erhelito/TIPE-LIFI/pics/IMG_20250205_171345.jpg

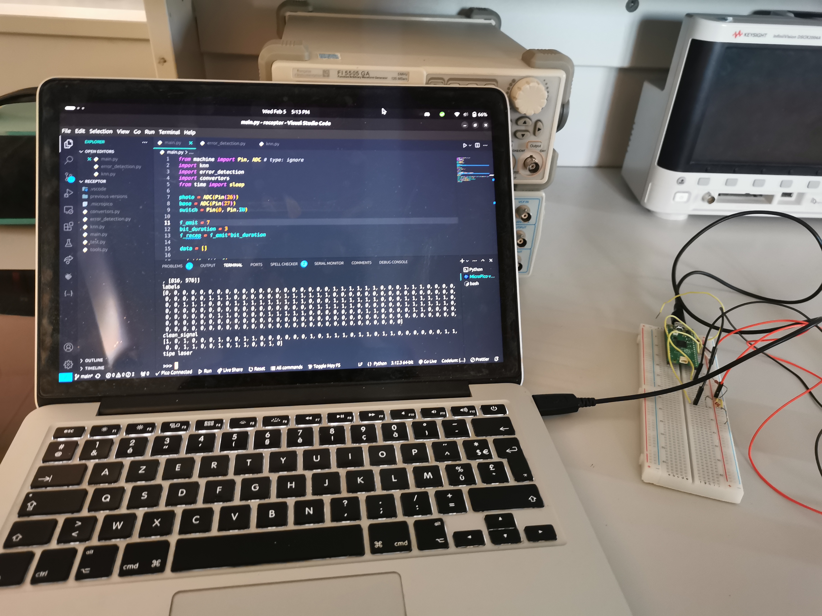
pics/IMG_20250205_171345.jpg
