erhelito/TIPE-LIFI/pics/IMG_20250509_170922.jpg

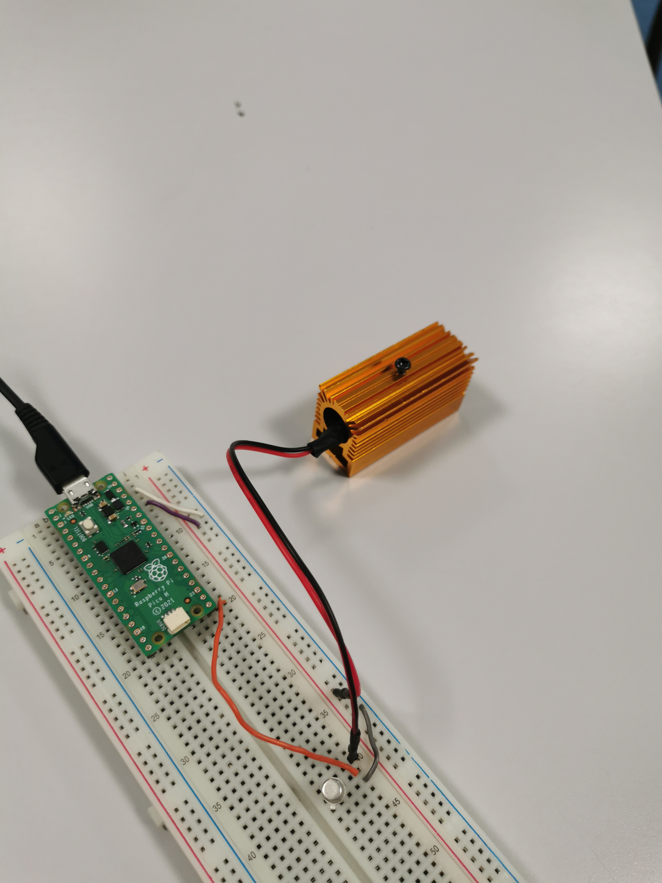
pics/IMG_20250509_170922.jpg
