erhelito/TIPE-LIFI/3D/supports.png

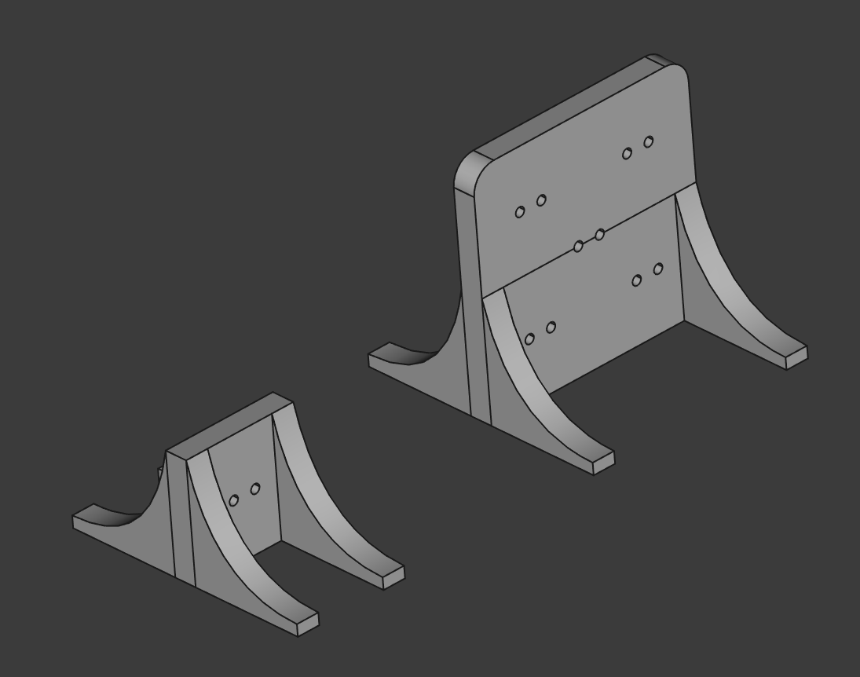
3D/supports.png
