erhelito/TIPE-LIFI/lifi elec/emitter.png

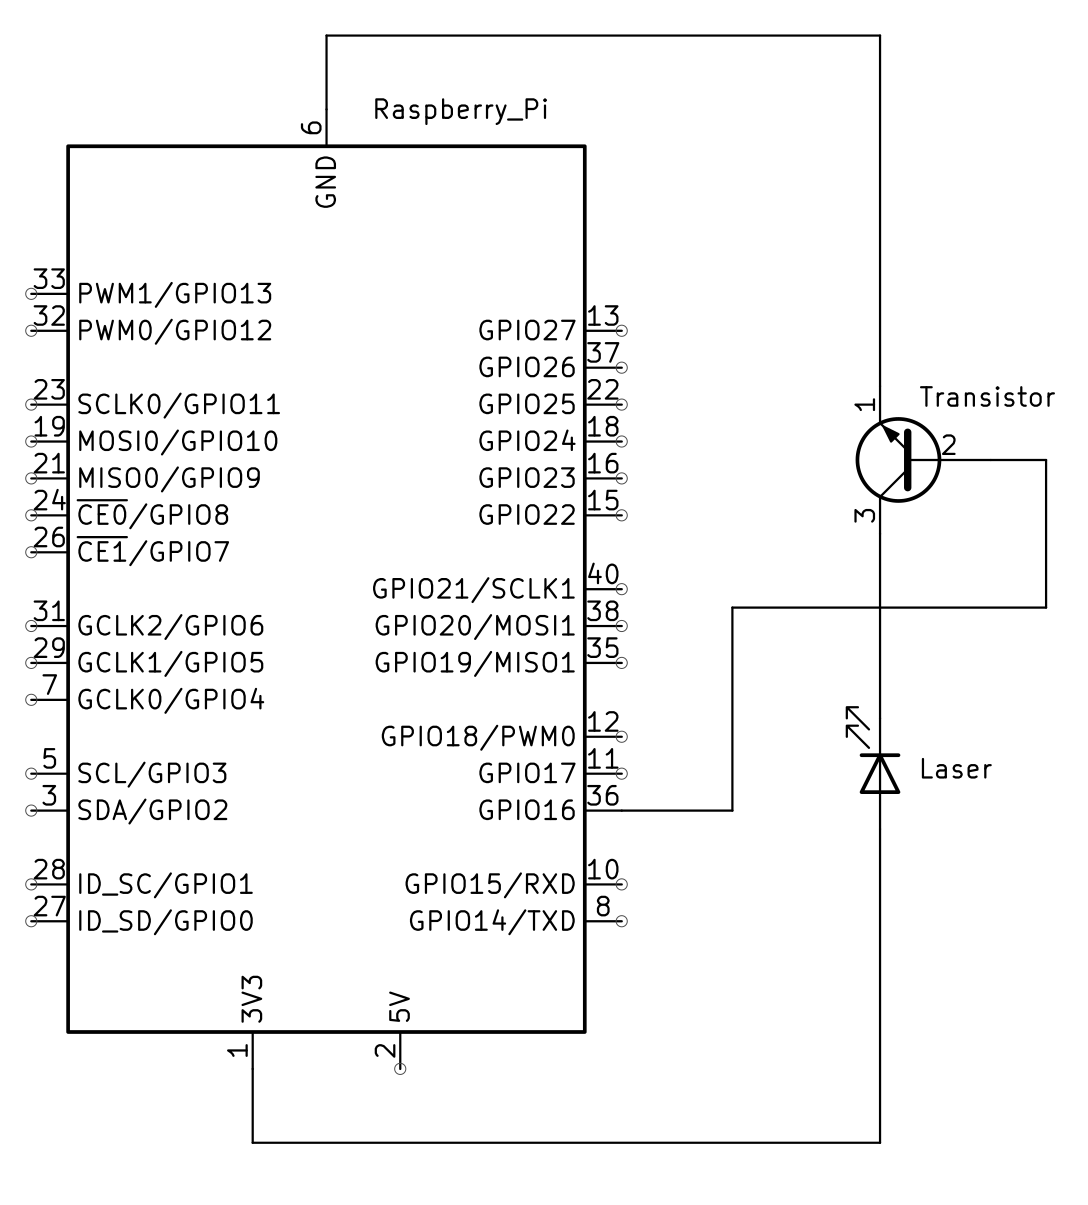
lifi elec/emitter.png
