erhelito/TIPE-LIFI/pics/IMG_20250129_170748.jpg

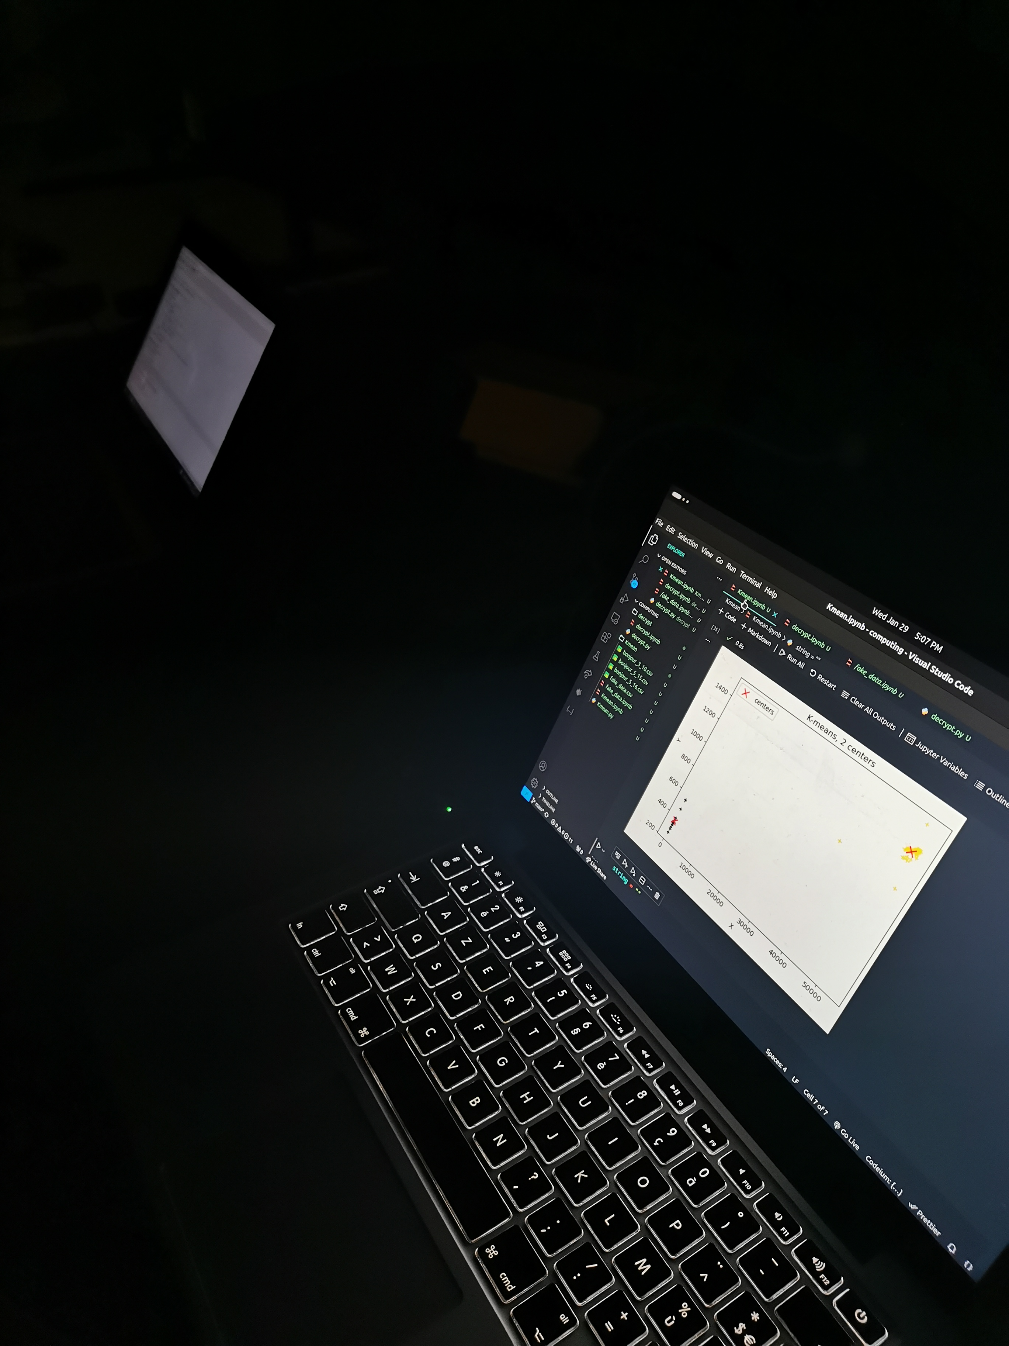
pics/IMG_20250129_170748.jpg
