erhelito/TIPE-LIFI/pics/IMG_20250129_170801.jpg

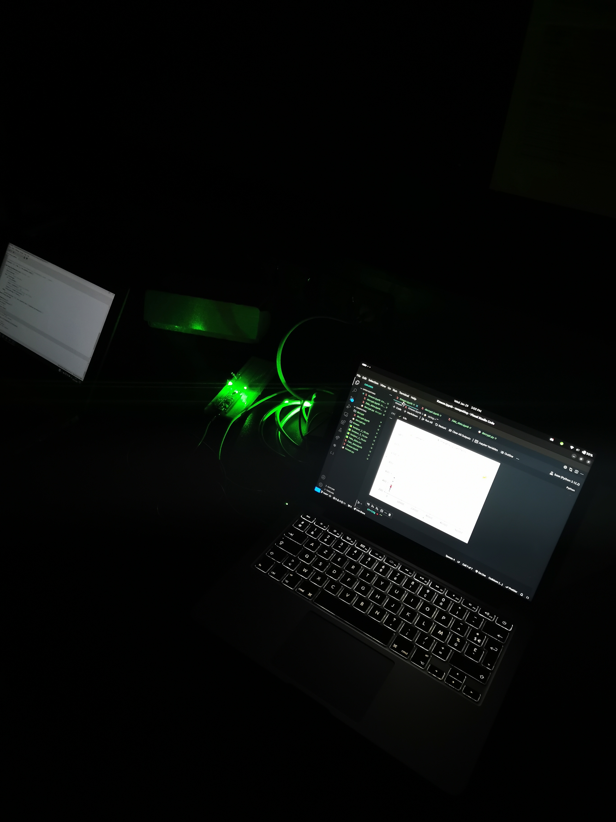
pics/IMG_20250129_170801.jpg
