erhelito/TIPE-LIFI/pics/IMG_20250129_170805.jpg

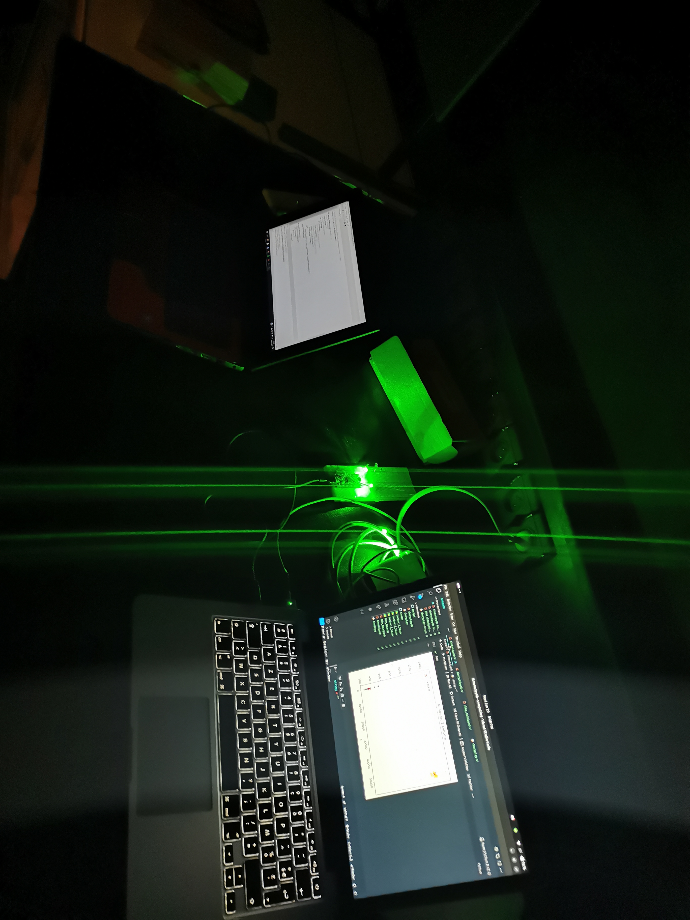
pics/IMG_20250129_170805.jpg
