erhelito/TIPE-LIFI/pics/IMG_20250205_155208.jpg

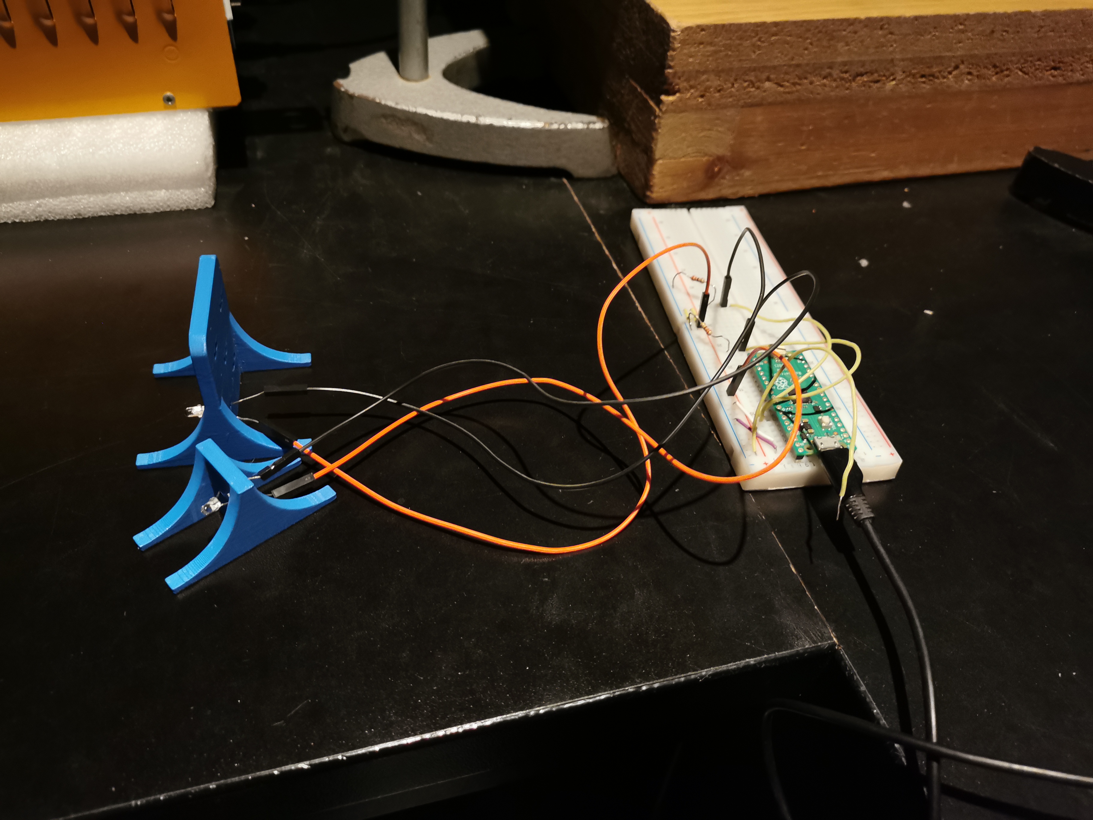
pics/IMG_20250205_155208.jpg
