erhelito/TIPE-LIFI/pics/IMG_20250205_171258.jpg

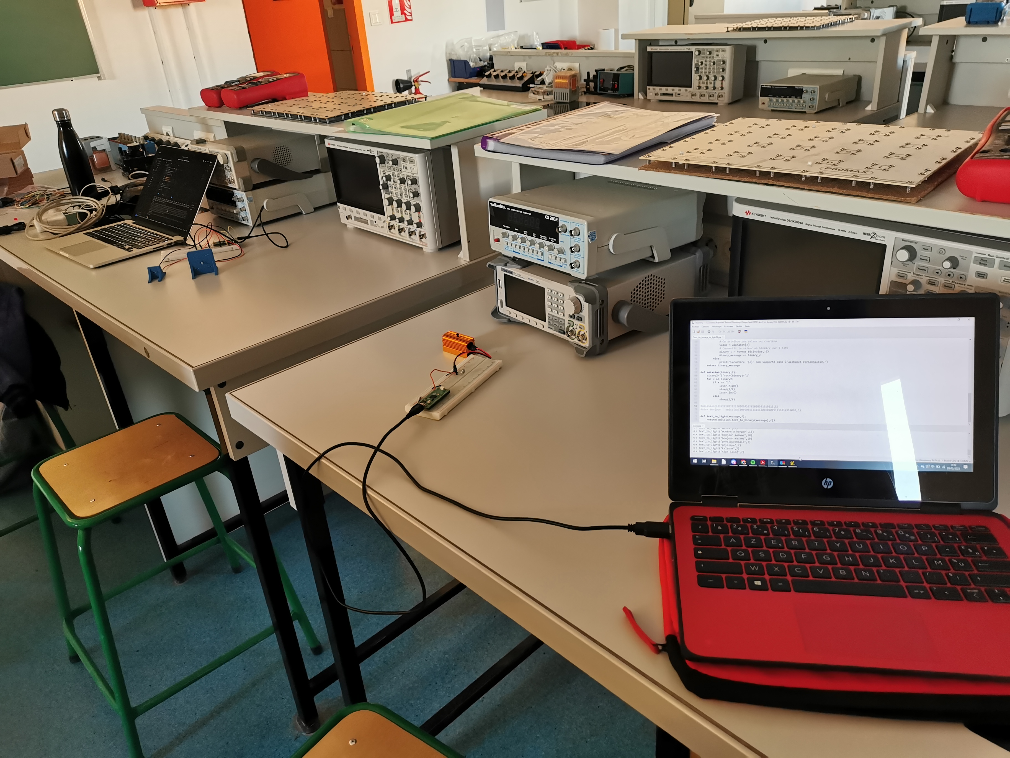
pics/IMG_20250205_171258.jpg
