erhelito/TIPE-LIFI/pics/IMG_20250205_171304.jpg

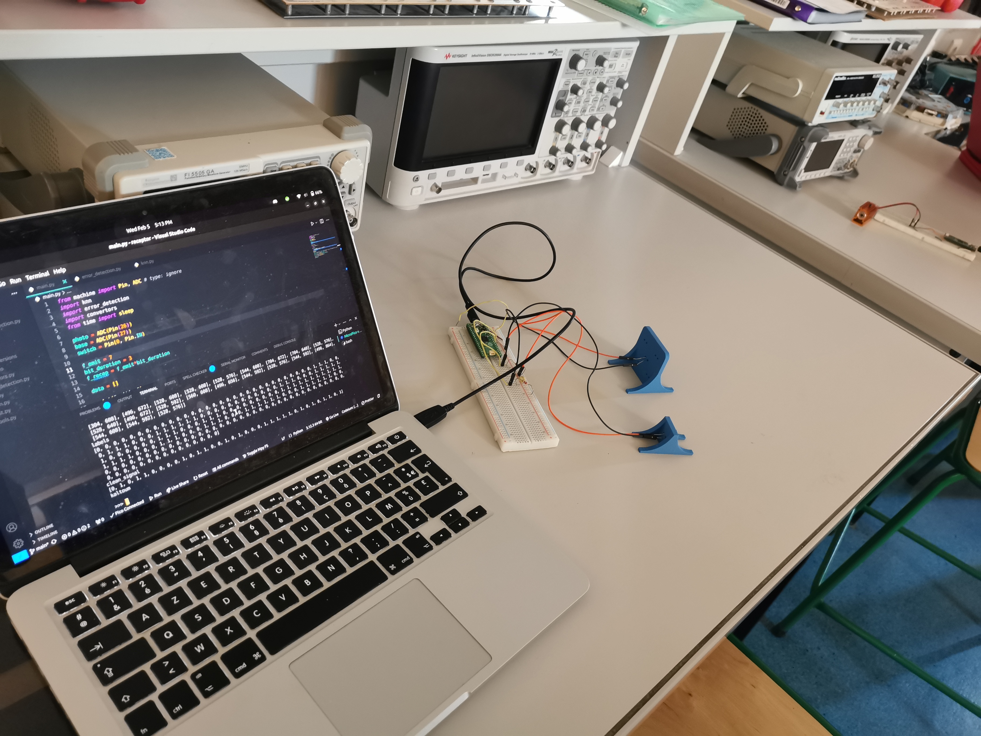
pics/IMG_20250205_171304.jpg
