erhelito/TIPE-LIFI/pics/IMG_20250205_171339.jpg

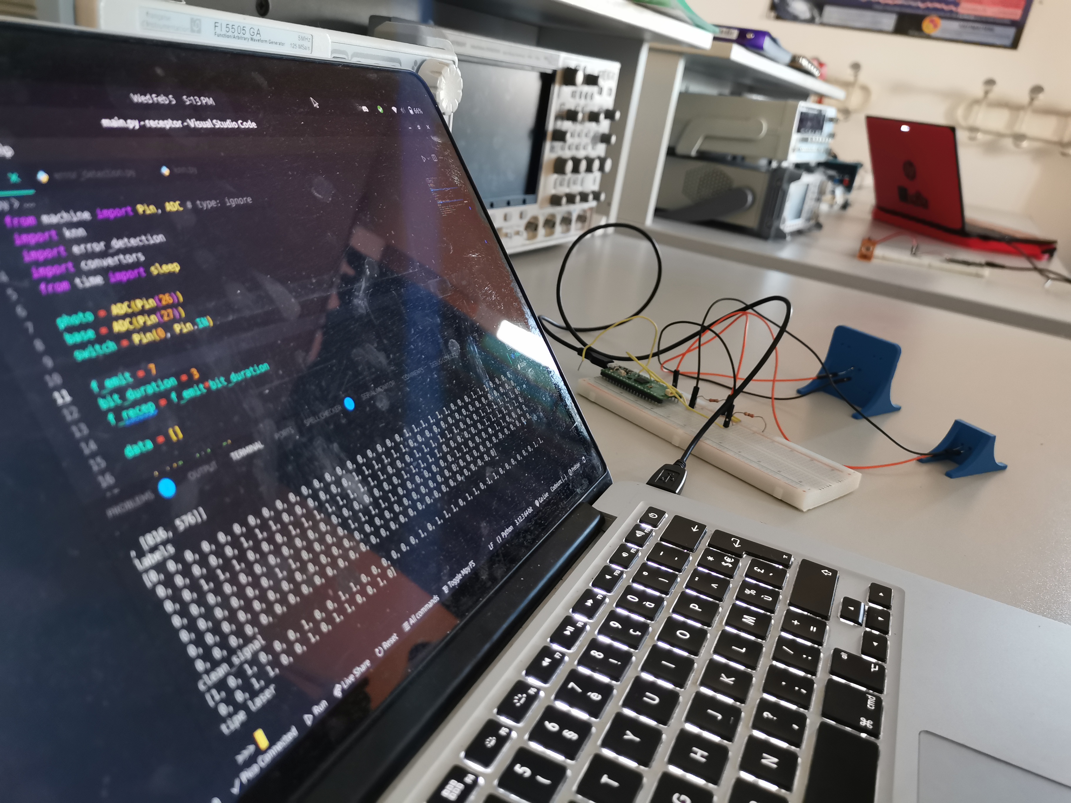
pics/IMG_20250205_171339.jpg
