erhelito/TIPE-LIFI/pics/IMG_20250205_171351.jpg

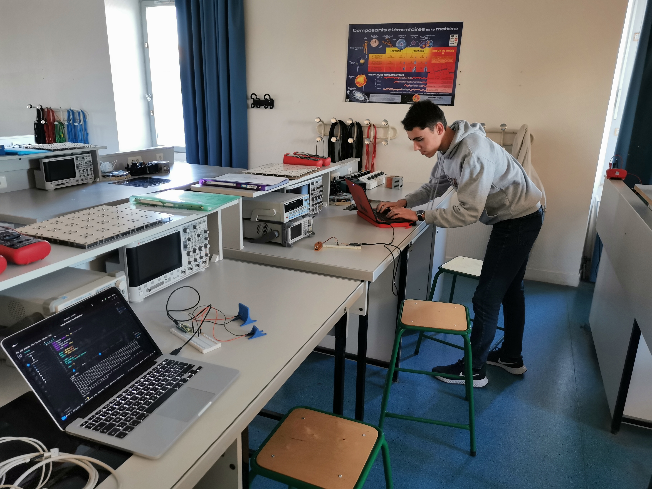
pics/IMG_20250205_171351.jpg
