erhelito/TIPE-LIFI/pics/IMG_20250212_154658.jpg

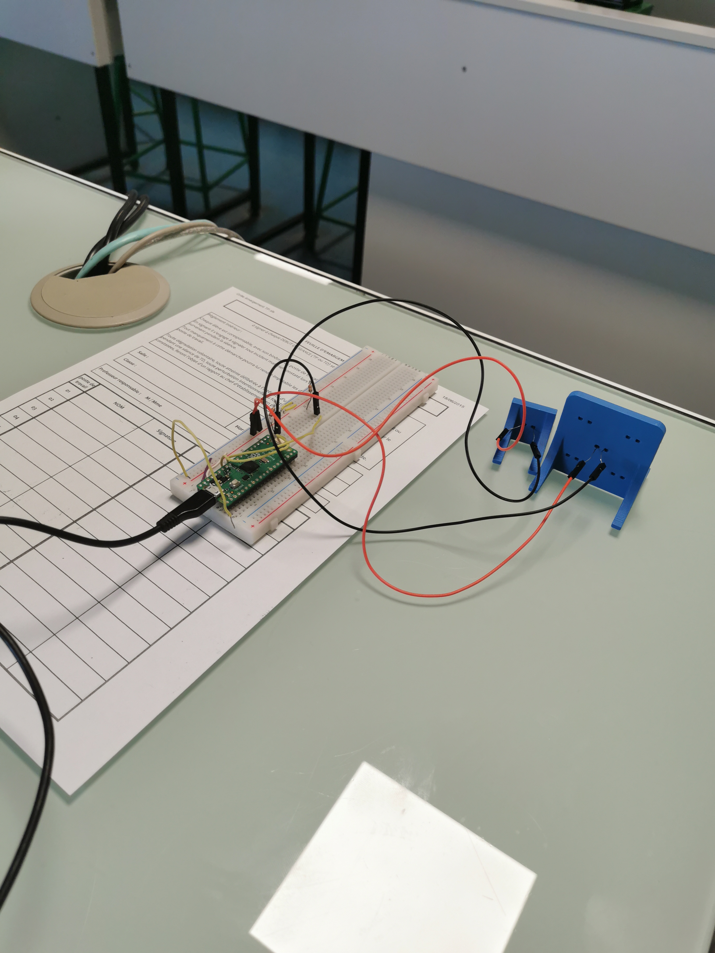
pics/IMG_20250212_154658.jpg
