erhelito/TIPE-LIFI/pics/IMG_20250212_154738.jpg

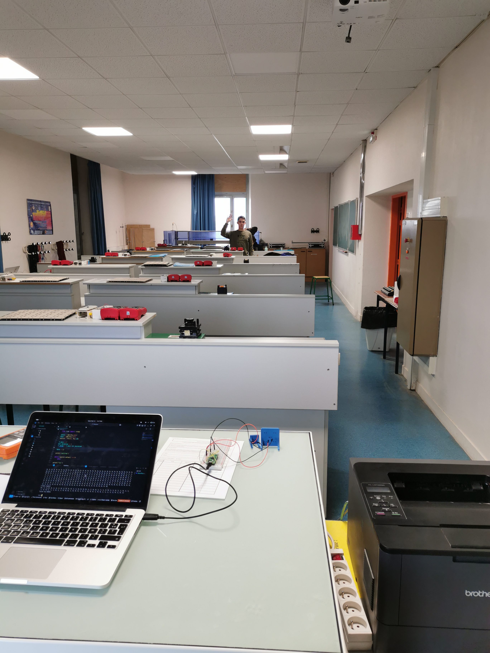
pics/IMG_20250212_154738.jpg
