erhelito/TIPE-LIFI/pics/IMG_20250212_160646.jpg

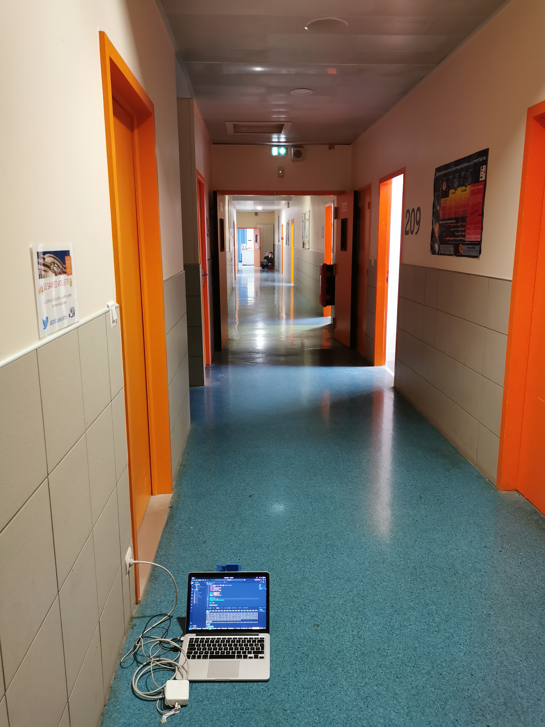
pics/IMG_20250212_160646.jpg
