erhelito/TIPE-LIFI/pics/IMG_20250305_170117.jpg

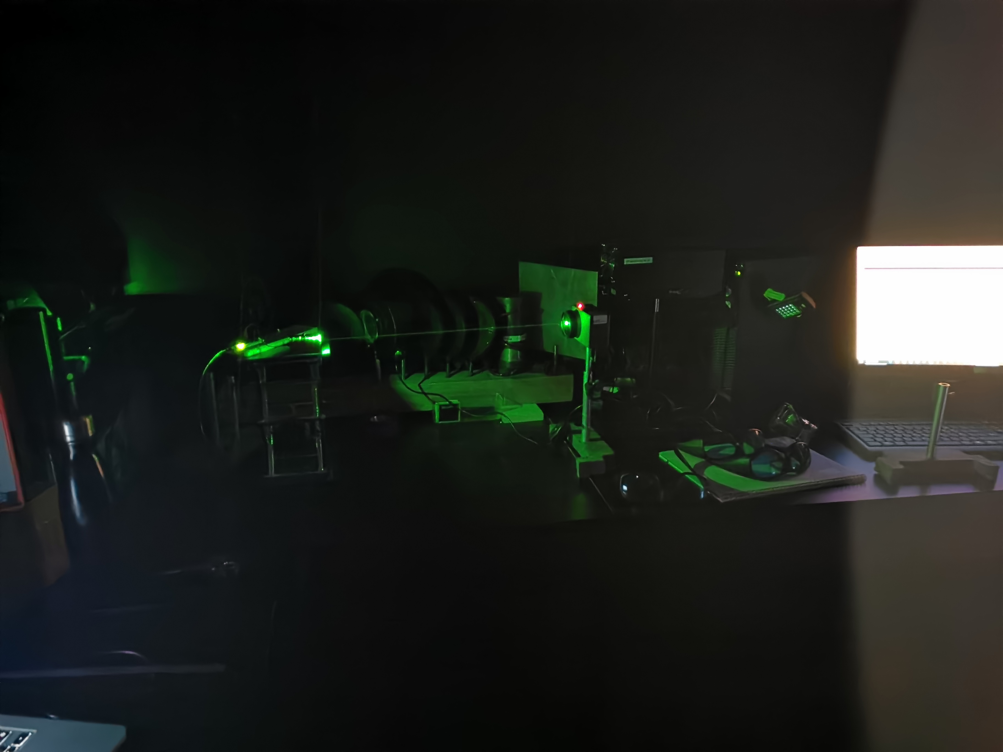
pics/IMG_20250305_170117.jpg
