erhelito/TIPE-LIFI/pics/IMG_20250319_162206.jpg

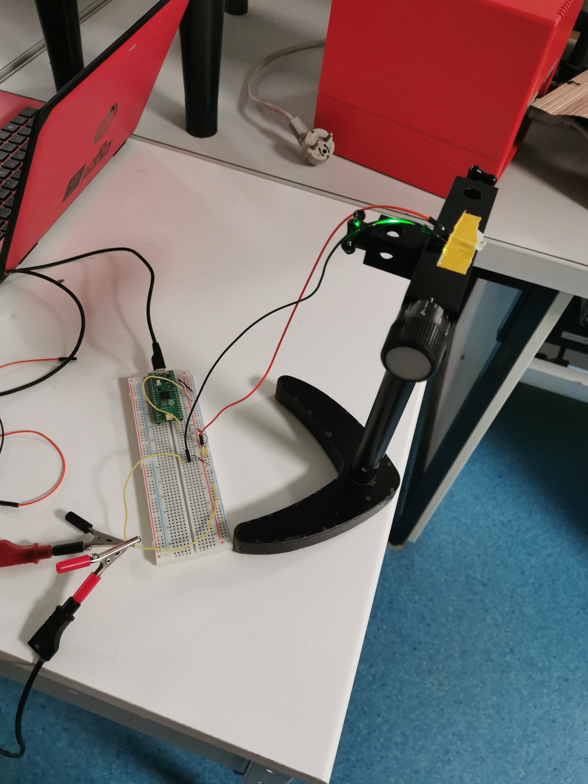
pics/IMG_20250319_162206.jpg
