erhelito/TIPE-LIFI/pics/IMG_20250319_162211.jpg

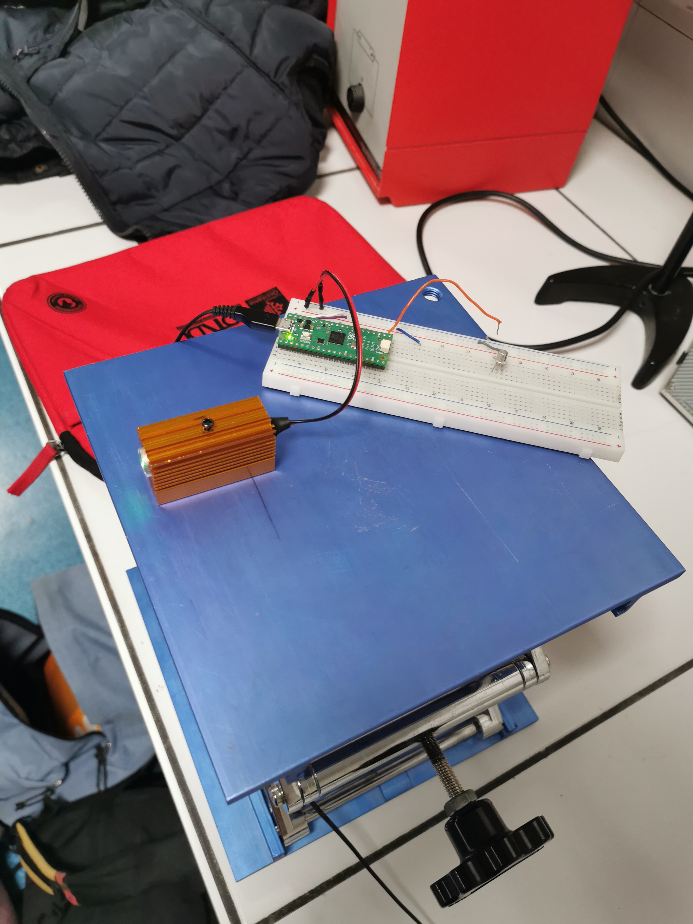
pics/IMG_20250319_162211.jpg
