erhelito/TIPE-LIFI/pics/IMG_20250319_164810.jpg

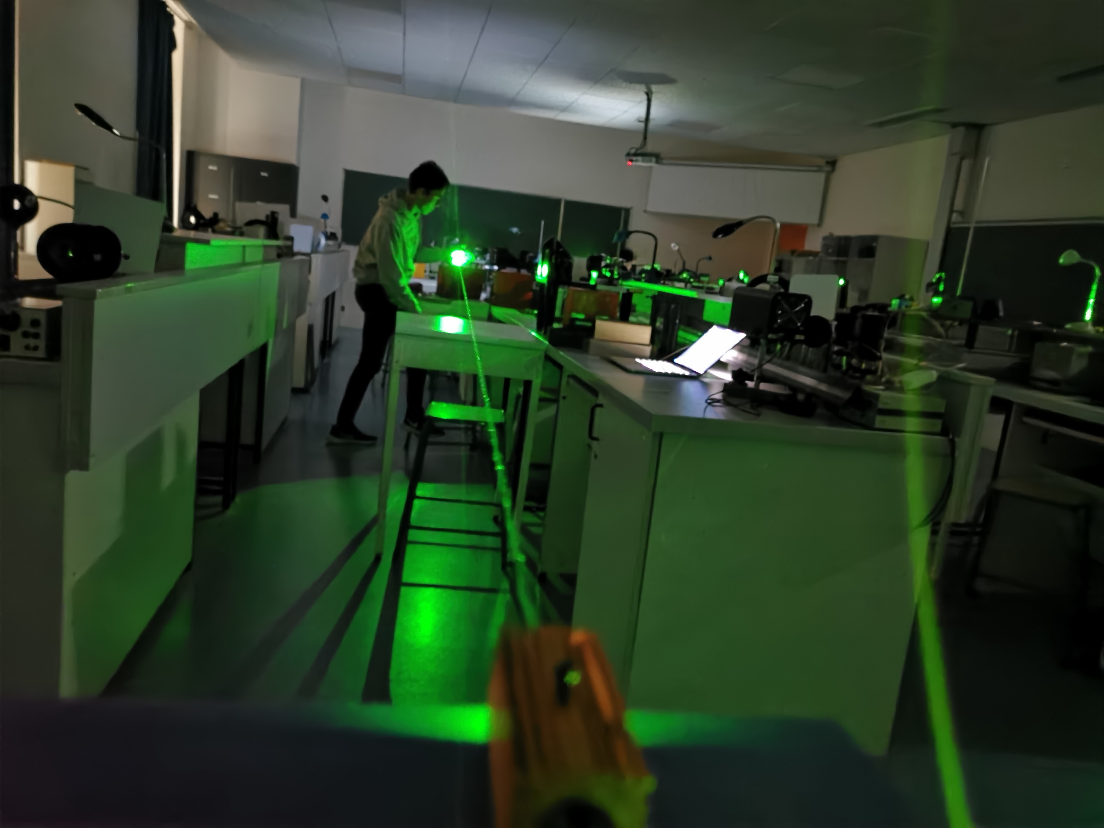
pics/IMG_20250319_164810.jpg
