erhelito/TIPE-LIFI/pics/IMG_20250509_170928.jpg

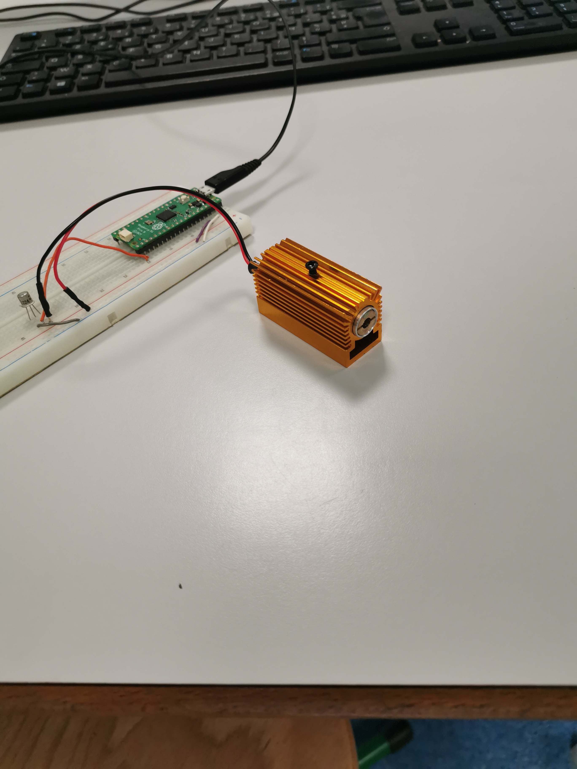
pics/IMG_20250509_170928.jpg
