erhelito/TIPE-LIFI/presentation/docs/reception.png

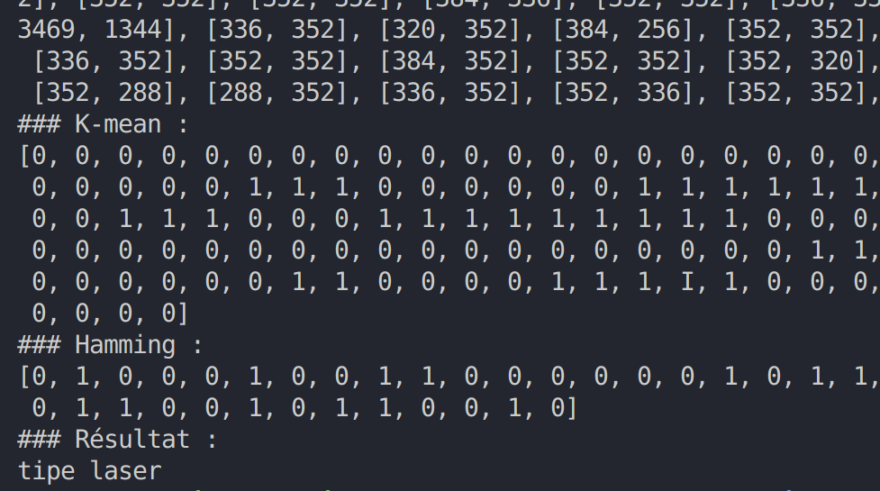
presentation/docs/reception.png
