erhelito/TIPE-LIFI/theory/laser/pics/div.png

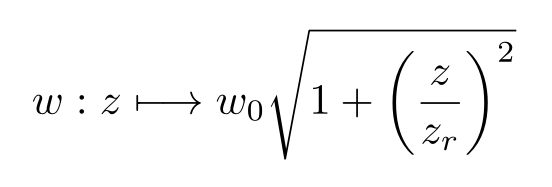
theory/laser/pics/div.png
