erhelito/TIPE-LIFI/theory/laser/pics/gauss.png

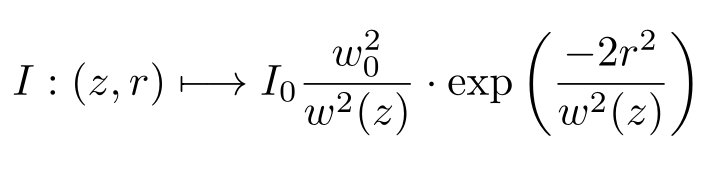
theory/laser/pics/gauss.png
