erhelito/TIPE-LIFI/theory/laser/pics/GaussianBeamWaist.jpg

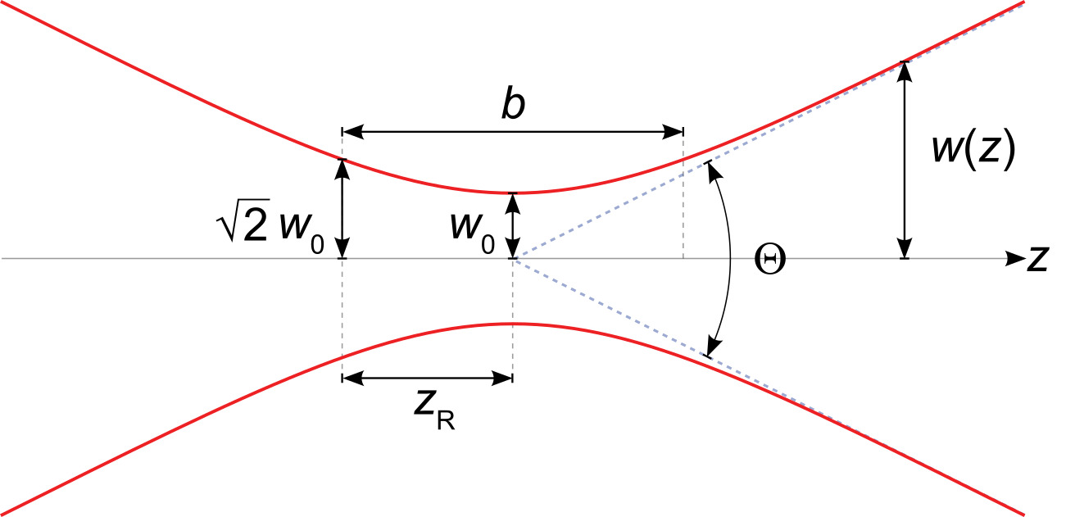
theory/laser/pics/GaussianBeamWaist.jpg
