erhelito/TIPE-LIFI/theory/laser/pics/Screenshot from 2025-05-09 09-58-38.png

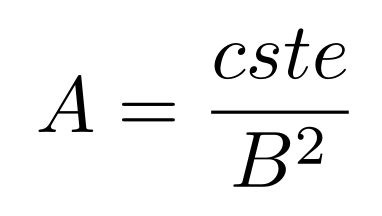
theory/laser/pics/Screenshot from 2025-05-09 09-58-38.png
