erhelito/TIPE-LIFI/theory/laser/pics/Screenshot from 2025-05-09 11-34-12.png

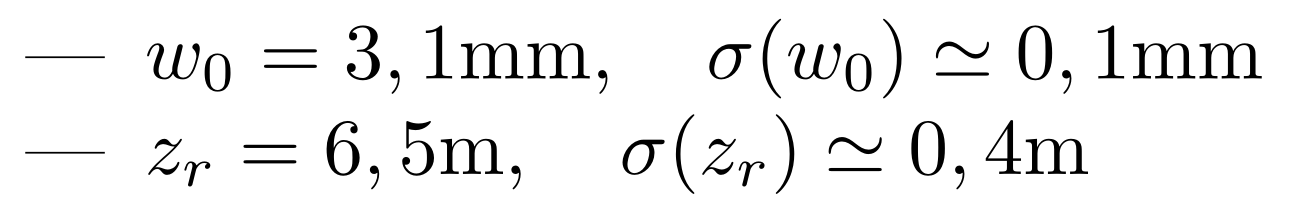
theory/laser/pics/Screenshot from 2025-05-09 11-34-12.png
