erhelito/TIPE-LIFI/theory/laser/pics/Screenshot from 2025-05-09 13-11-44.png

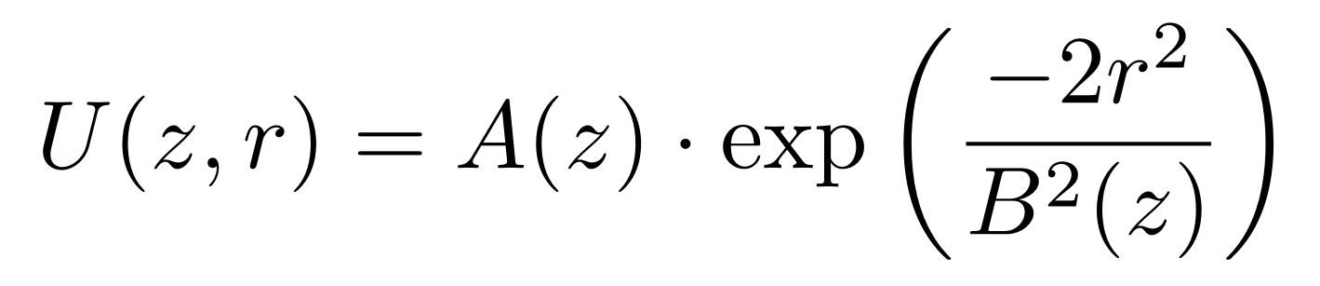
theory/laser/pics/Screenshot from 2025-05-09 13-11-44.png
