erhelito/TIPE-LIFI/theory/laser/pics/Screenshot from 2025-05-09 13-16-56.png

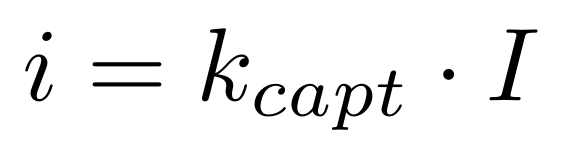
theory/laser/pics/Screenshot from 2025-05-09 13-16-56.png
