erhelito/TIPE-LIFI/prog/receptor/V3/knn.py

from math import sqrt

def distance(p1, p2):
    return sqrt((p1[0] - p2[0]) ** 2 + (p1[1] - p2[1]) ** 2)

def k_means(data, centers, n=100):
    n_points = len(data)
    n_clusters = len(centers)
    
    labels = [0]*n_points
    
    for _ in range(n):
        # update labels
        new_labels = []
        for i in range(n_points):
            # compute all distances, attribute new centers
            distances = [distance(data[i], center) for center in centers]
            new_labels.append(distances.index(min(distances)))

        # update clusters
        new_centers = []
        for k in range(n_clusters):
            cluster_points = [data[i] for i in range(n_points) if new_labels[i] == k]
            if cluster_points != []: # for not empty clusters
                mean_x = sum(point[0] for point in cluster_points) / len(cluster_points)
                mean_y = sum(point[1] for point in cluster_points) / len(cluster_points)
                new_centers.append([mean_x, mean_y])

            else: # for empty clusters
                new_centers.append(centers[k])
        
        # check for convergence
        if new_centers == centers:
            break
        centers = new_centers
        labels = new_labels

    print("labels")
    print(labels)

    return centers, labels
